olkb/olkb_parts/planck/lo-pro-plate-mx-2x2u.stl

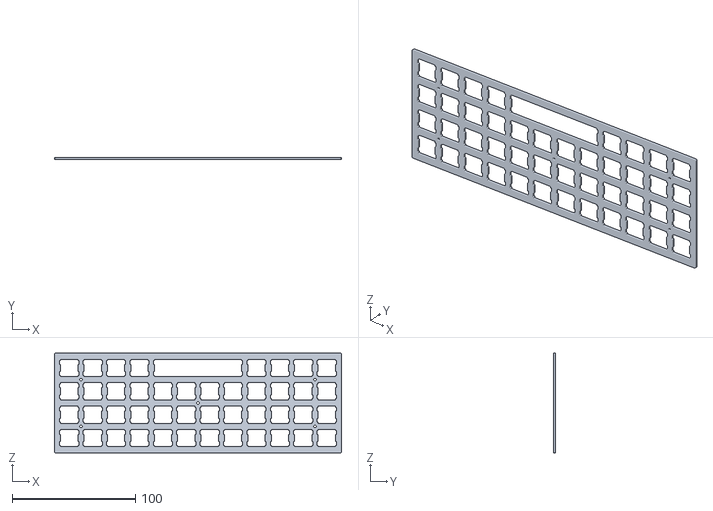
[picture p17: CAD file, 2018-10-09]
planck/lo-pro-plate-mx-2x2u.stl
233.0 x 1.54 x 81.0
