olkb/olkb_parts/planck/middles/MIDPLK50-12.stl

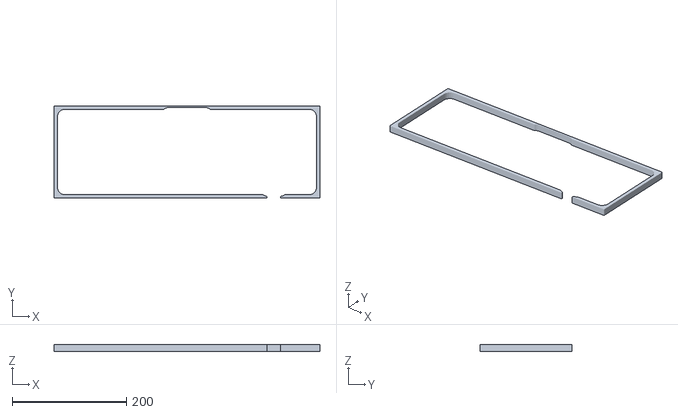
[picture p18: CAD file, 2015-04-01]
planck/middles/MIDPLK50-12.stl
466.0 x 162.0 x 12.0
