olkb/olkb_parts/planck/tops/TOPGRD50.dxf

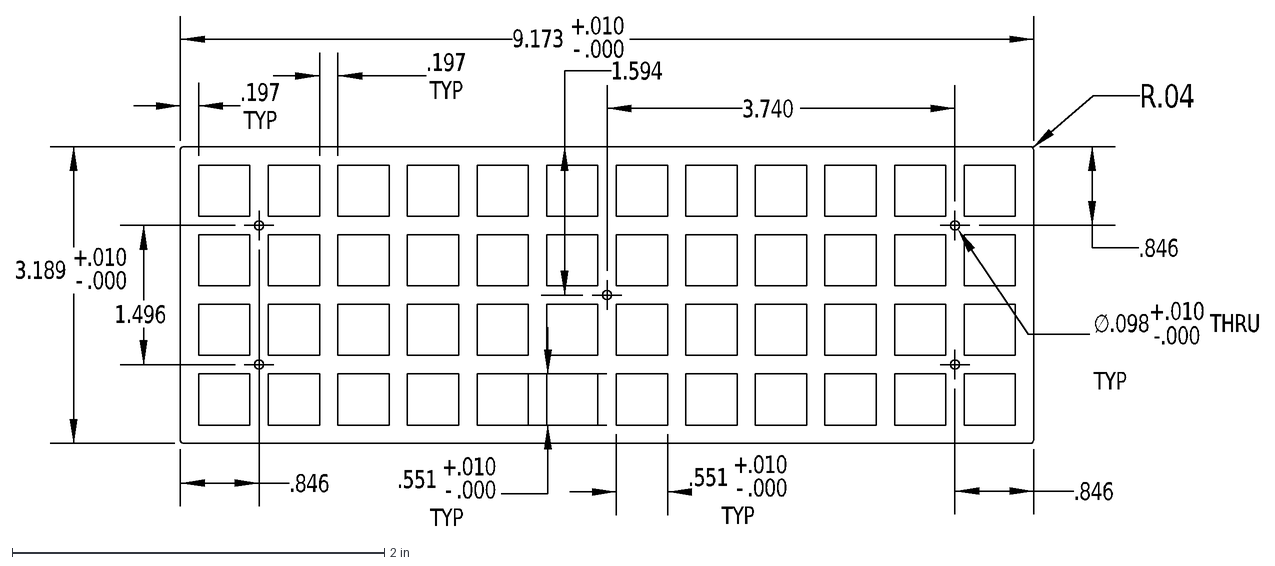
[picture p19: CAD file, 2016-04-22]
planck/tops/TOPGRD50.dxf
9.173
+
-
.010
.000
3.189
∅.098+.010^-.000 THRU TYP
.551
TYP
.197
.846
3.740
1.496
1.594
R.04
