olkb/olkb_parts/preonic/preonic-rev3-hipro-mod.stl

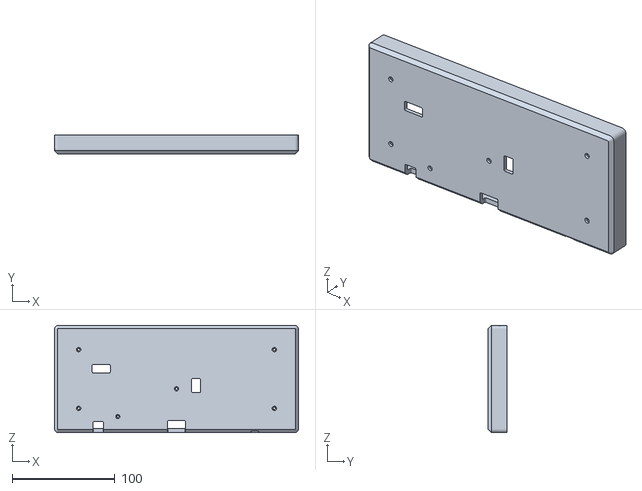
[picture p20: CAD file, 2019-12-29]
preonic/preonic-rev3-hipro-mod.stl
237.0 x 18.1 x 104.0
