olkb/olkb_parts/atomic/tops/TOPJCK50.dxf

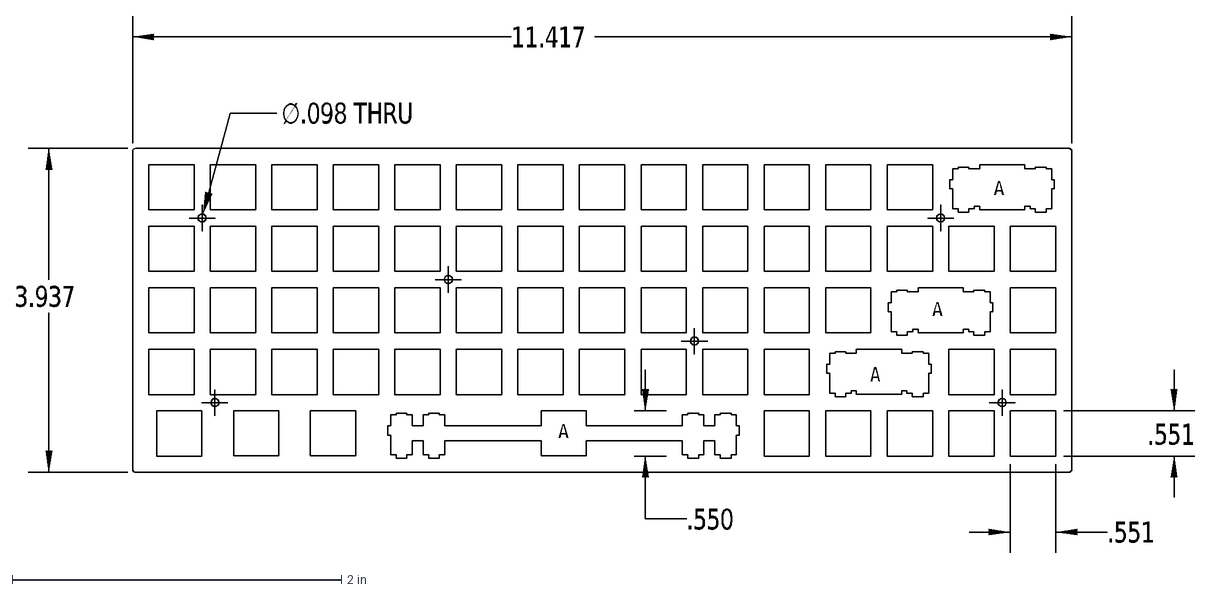
[picture p21: CAD file, 2016-04-22]
atomic/tops/TOPJCK50.dxf
A
11.417
3.937
.551
.550
∅.098 THRU
