olkb/olkb_parts/others/TOPNEU50.dxf

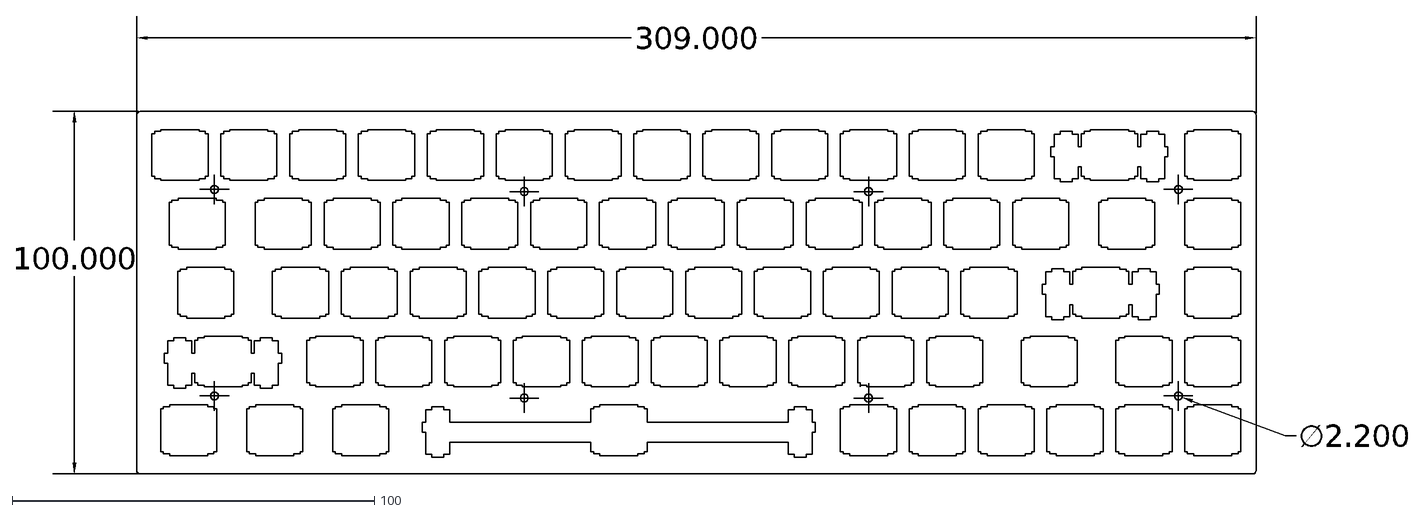
[picture p22: CAD file, 2016-04-22]
others/TOPNEU50.dxf
309.000
100.000
∅2.200
