olkb/olkb_parts/planck/hi-pro-plate-mx.stl

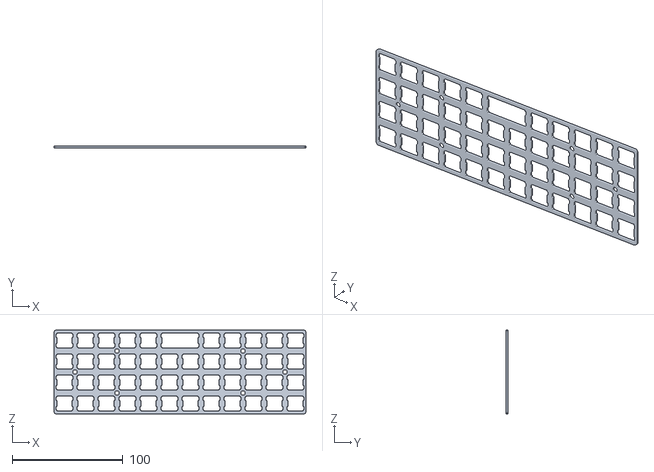
[picture p23: CAD file, 2018-06-27]
planck/hi-pro-plate-mx.stl
228.0 x 1.54 x 76.0
