olkb/olkb_parts/planck/lo-pro-covers/case-cover-plain.stl

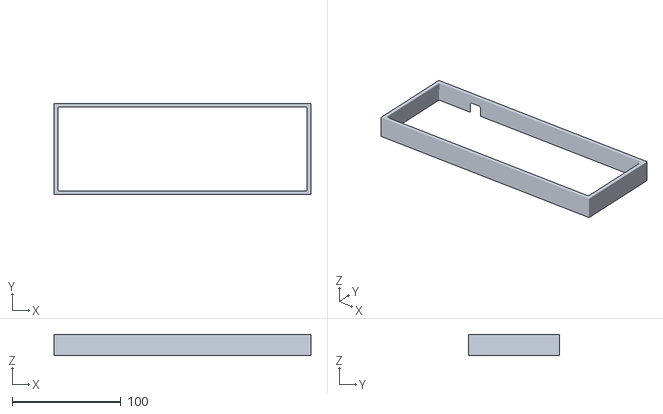
[picture p24: CAD file, 2017-01-22]
planck/lo-pro-covers/case-cover-plain.stl
236.0 x 84.0 x 19.5
