olkb/olkb_parts/planck/middles/MIDPLK50-14.stl

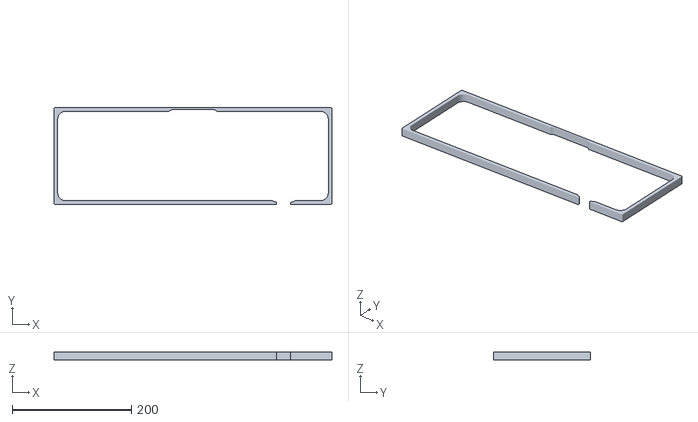
[picture p25: CAD file, 2015-04-01]
planck/middles/MIDPLK50-14.stl
466.0 x 162.0 x 14.0
