olkb/olkb_parts/planck/tops/TOPMIT50.dxf

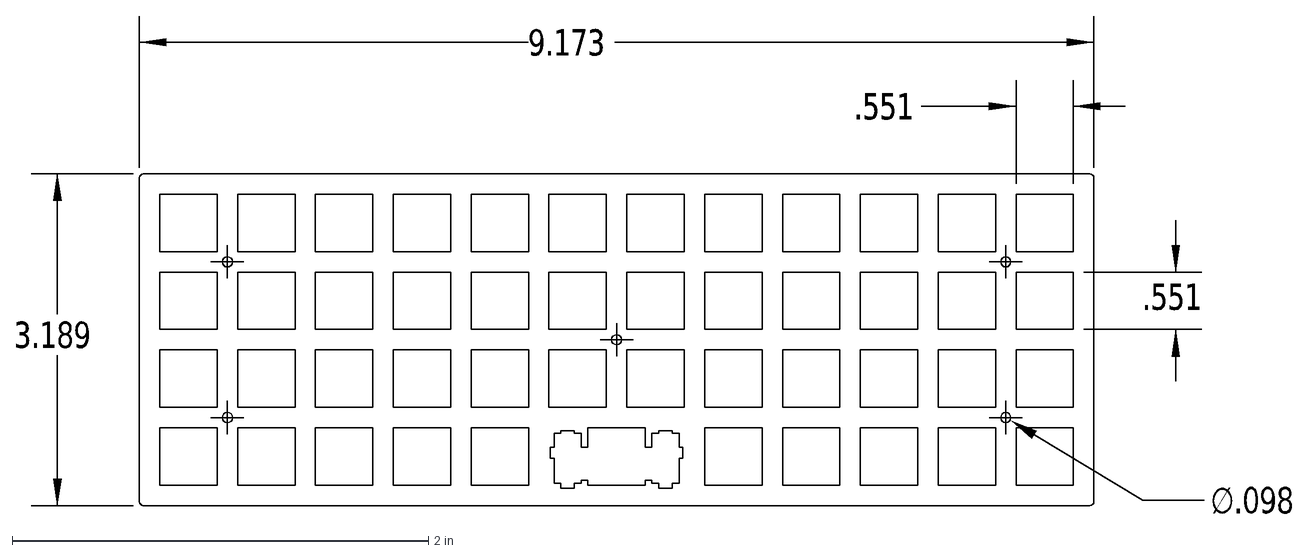
[picture p26: CAD file, 2016-04-22]
planck/tops/TOPMIT50.dxf
9.173
3.189
∅.098
.551
