olkb/olkb_parts/preonic/PRE-END.stl

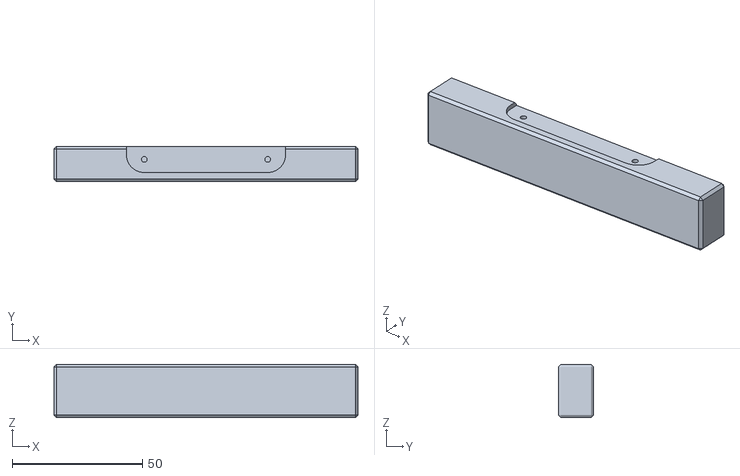
[picture p27: CAD file, 2019-11-19]
preonic/PRE-END.stl
116.5 x 13.5 x 20.5
