olkb/olkb_parts/atomic/tops/TOPASK50.dxf

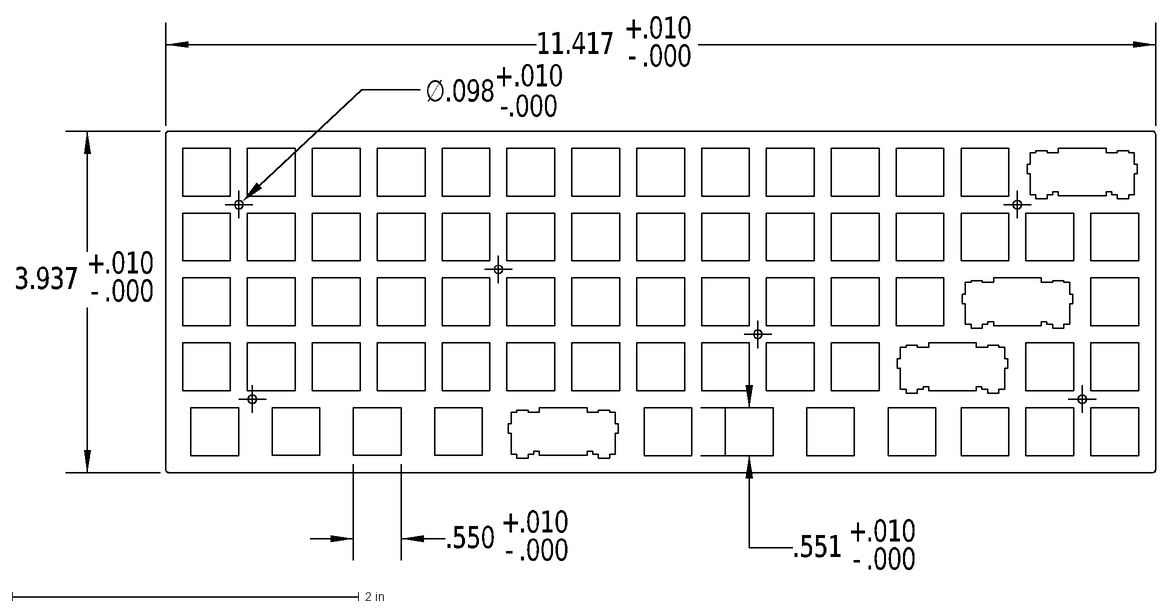
[picture p28: CAD file, 2016-04-22]
atomic/tops/TOPASK50.dxf
11.417
+
-
.010
.000
3.937
.550
.551
∅.098+.010^-.000
