olkb/olkb_parts/others/TOPQUA50.dxf

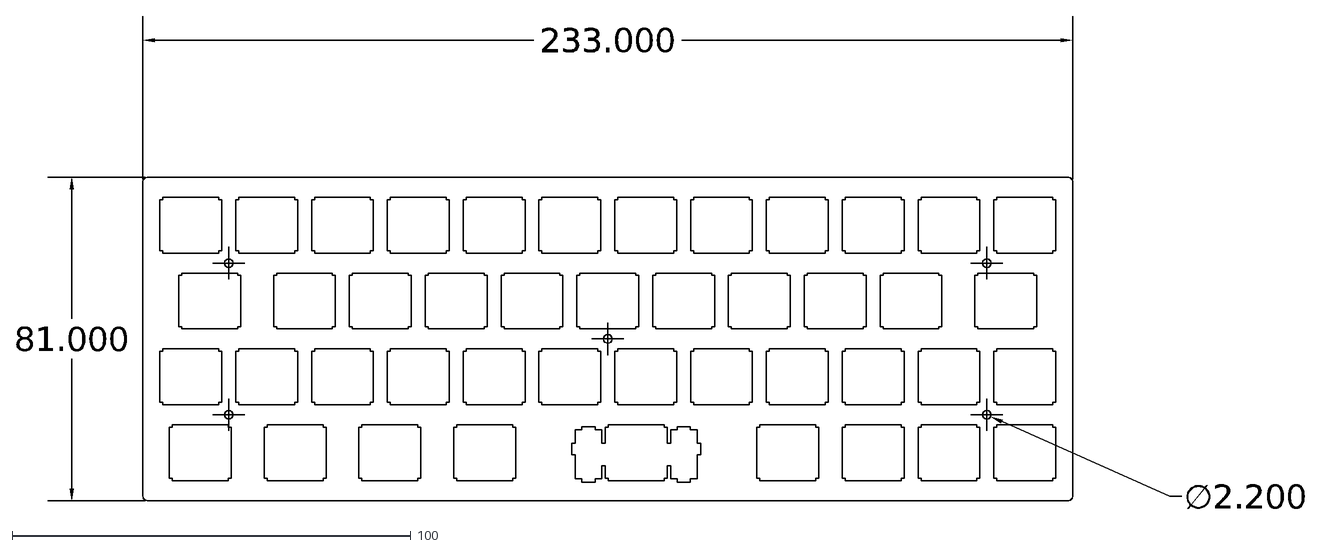
[picture p29: CAD file, 2016-04-22]
others/TOPQUA50.dxf
233.000
81.000
∅2.200
