olkb/olkb_parts/planck/lo-pro-covers/case-cover-high.stl

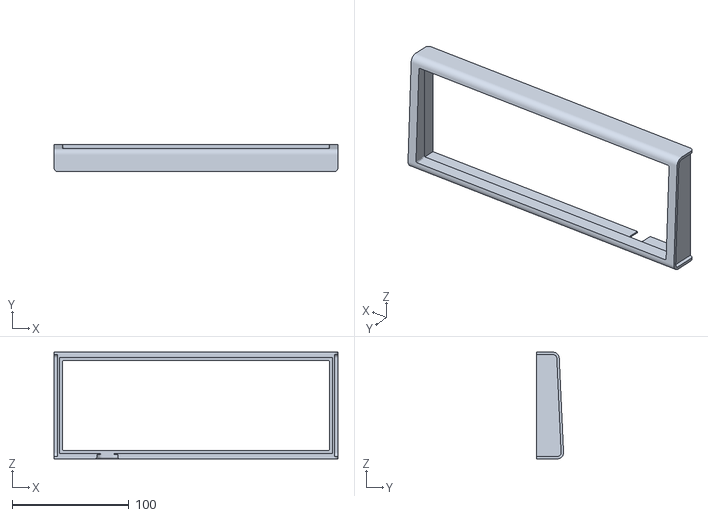
[picture p30: CAD file, 2017-01-06]
planck/lo-pro-covers/case-cover-high.stl
243.4 x 23.3 x 91.4
