olkb/olkb_parts/planck/middles/MIDPLK50-10.stl

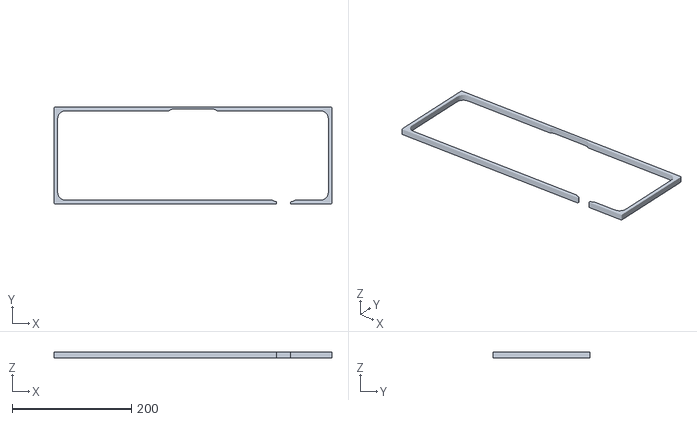
[picture p31: CAD file, 2015-03-30]
planck/middles/MIDPLK50-10.stl
466.0 x 162.0 x 10.00
