olkb/olkb_parts/planck/tops/TOPPMU50.dxf

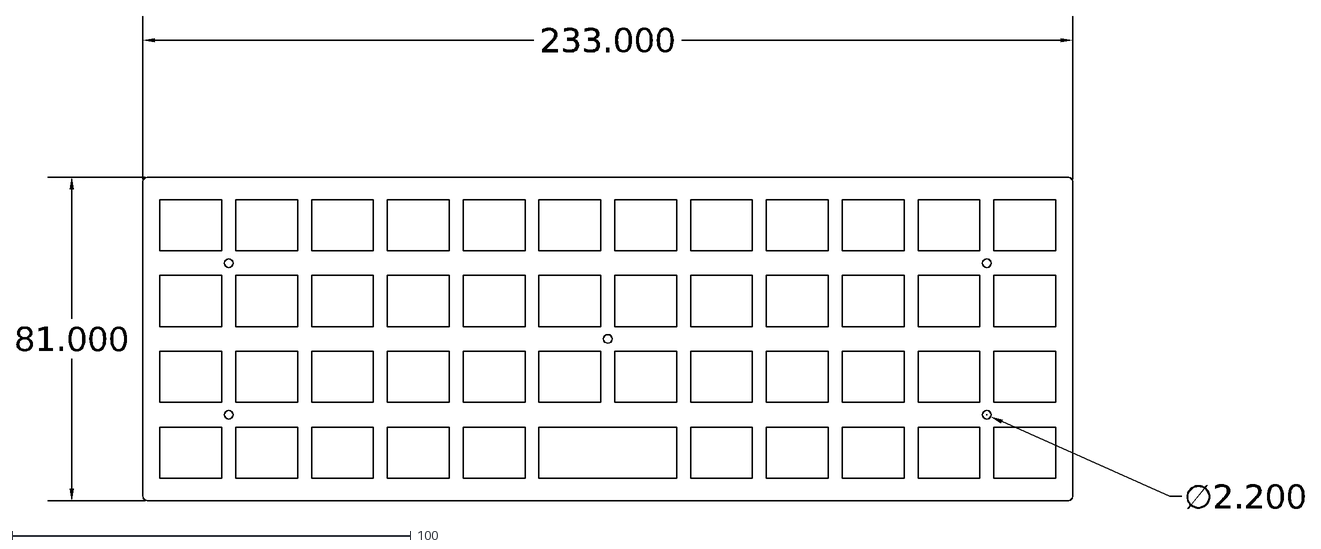
[picture p32: CAD file, 2016-04-22]
planck/tops/TOPPMU50.dxf
233.000
81.000
∅2.200
