olkb/olkb_parts/preonic/hi-pro-plate-mx-2x2u.stl

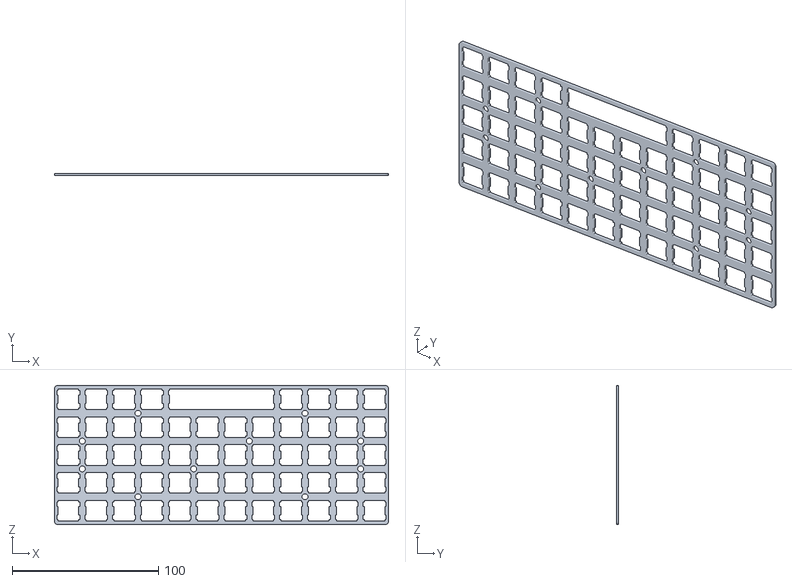
[picture p33: CAD file, 2018-06-27]
preonic/hi-pro-plate-mx-2x2u.stl
228.0 x 1.54 x 95.0
