olkb/olkb_parts/atomic/tops/TOPMLO50.dxf

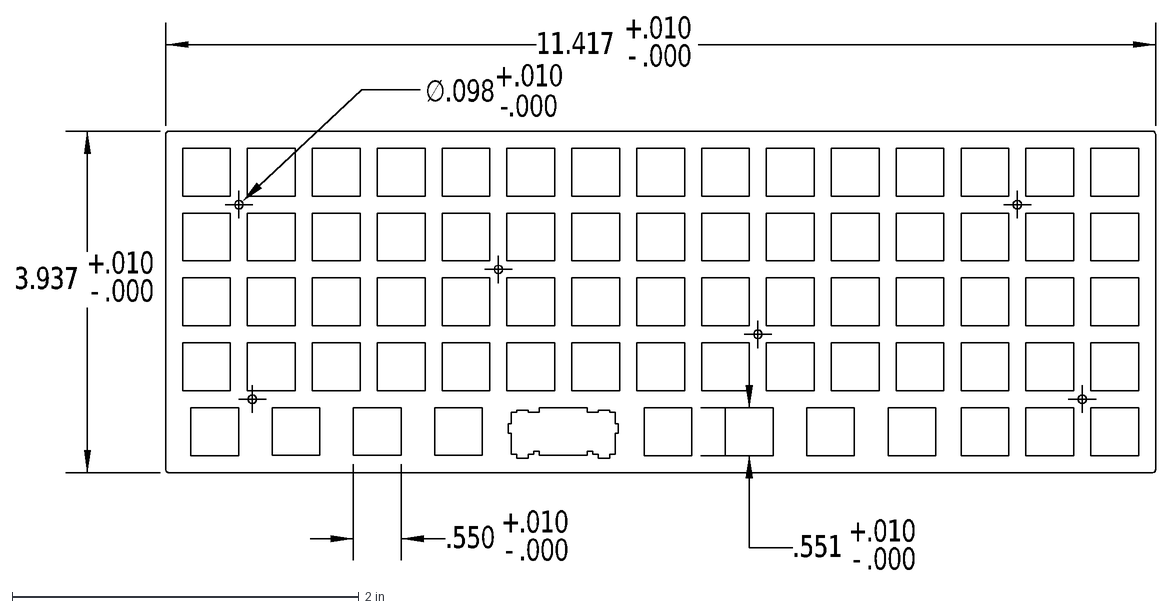
[picture p34: CAD file, 2016-04-22]
atomic/tops/TOPMLO50.dxf
11.417
+
-
.010
.000
3.937
.550
.551
∅.098+.010^-.000
