olkb/olkb_parts/planck/hi-pro-plate-matias.stl

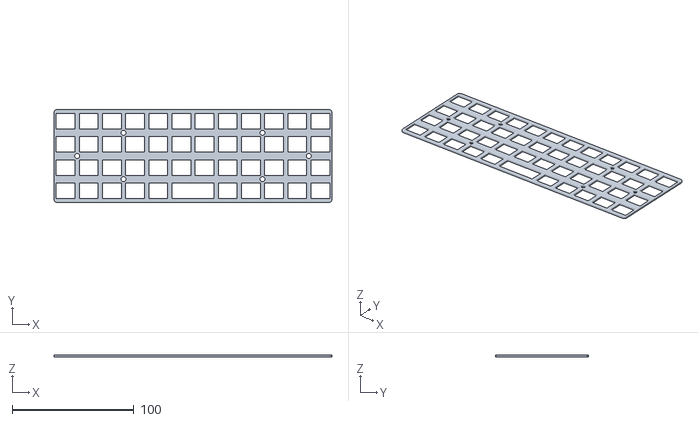
[picture p35: CAD file, 2018-06-27]
planck/hi-pro-plate-matias.stl
228.0 x 76.0 x 1.54
