olkb/olkb_parts/planck/tops/TOPPUN50.dxf

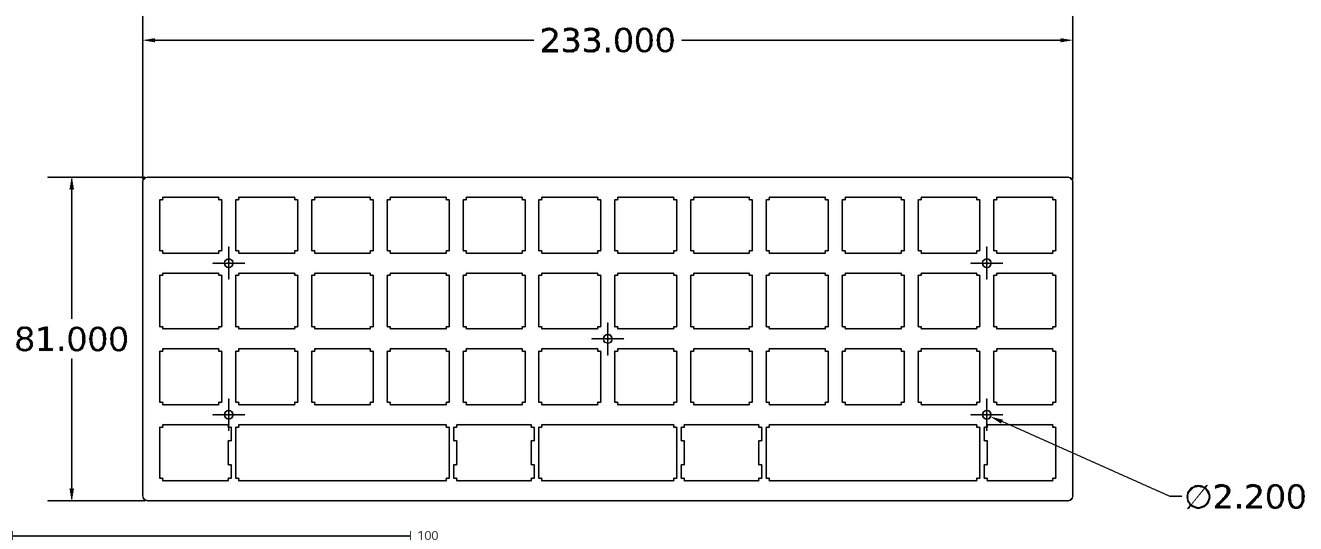
[picture p36: CAD file, 2016-04-22]
planck/tops/TOPPUN50.dxf
233.000
81.000
∅2.200
