olkb/olkb_parts/atomic/tops/TOPMAU50.dxf

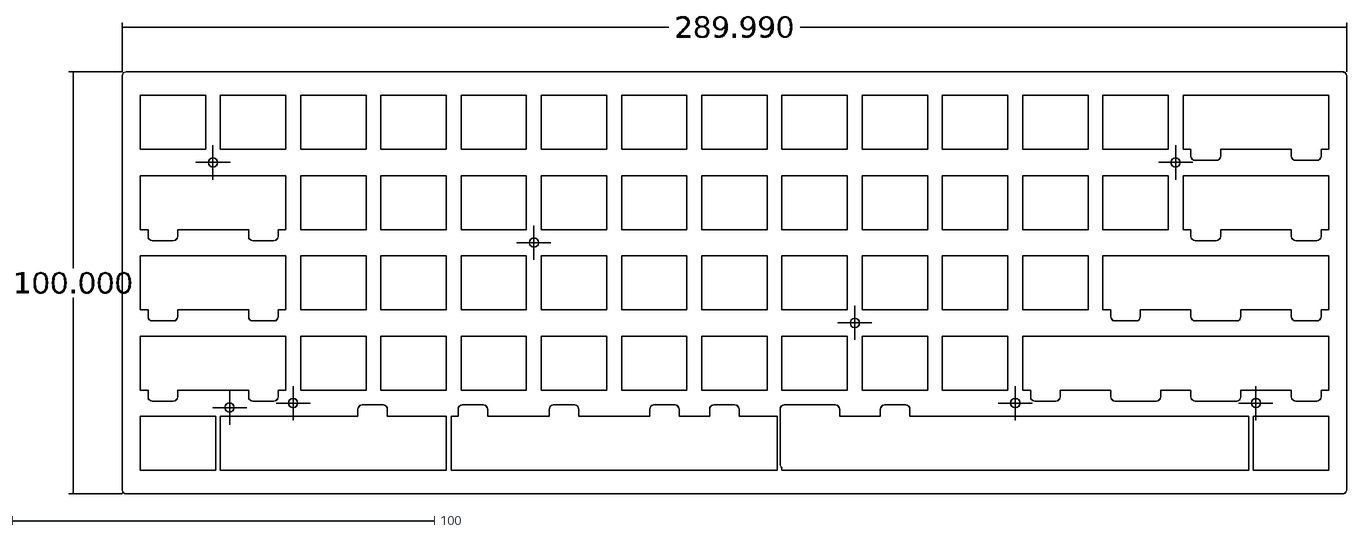
[picture p37: CAD file, 2016-04-22]
atomic/tops/TOPMAU50.dxf
289.990
100.000
