olkb/olkb_parts/planck/hi-pro-bottom.stl

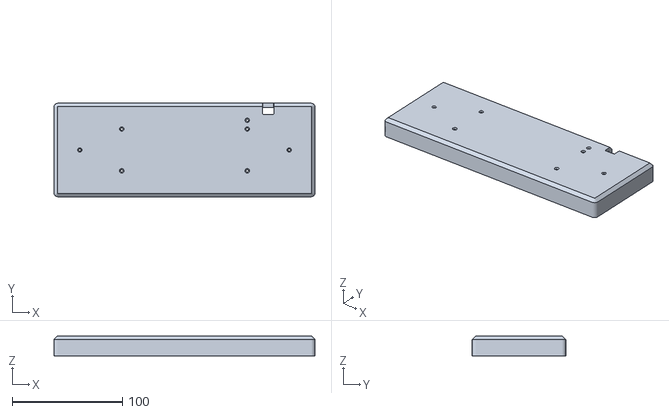
[picture p38: CAD file, 2018-06-27]
planck/hi-pro-bottom.stl
237.0 x 85.0 x 18.1
