olkb/olkb_parts/atomic/tops/TOPAUN50.dxf

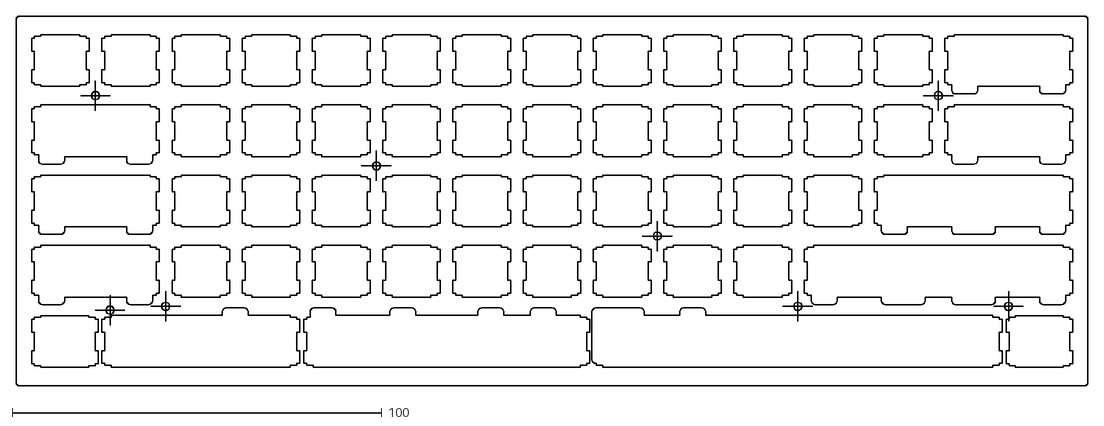
[picture p39: CAD file, 2016-04-22]
atomic/tops/TOPAUN50.dxf
290.0 x 100.0
