olkb/olkb_parts/planck/hi-pro-bottom-mod.stl

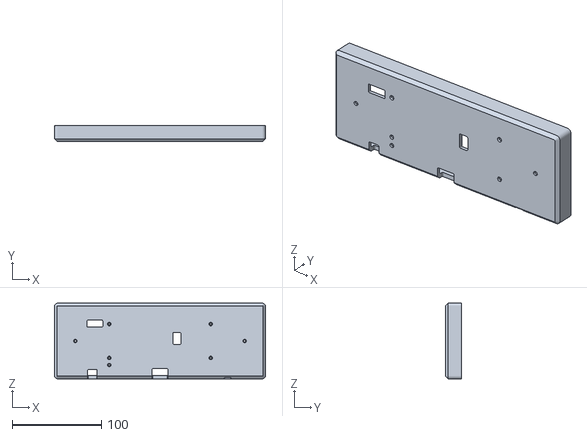
[picture p40: CAD file, 2018-06-27]
planck/hi-pro-bottom-mod.stl
237.0 x 18.1 x 85.0
