olkb/olkb_parts/preonic/hi-pro-bottom-rev3.stl

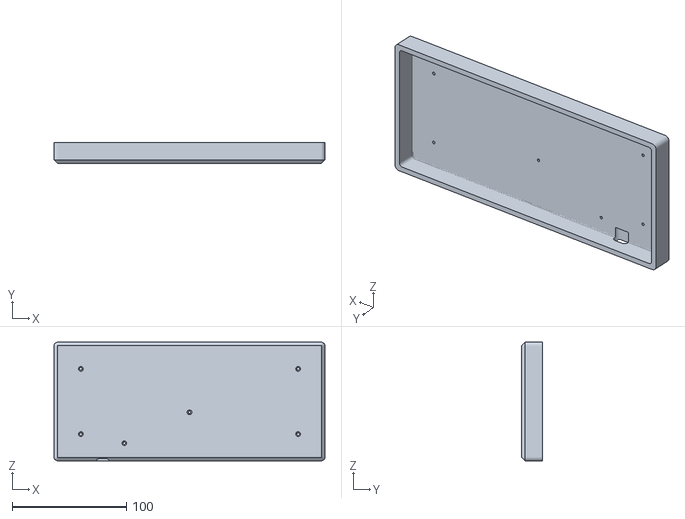
[picture p41: CAD file, 2018-06-27]
preonic/hi-pro-bottom-rev3.stl
237.0 x 18.1 x 104.0
