olkb/olkb_parts/planck/bottom-plate.dxf

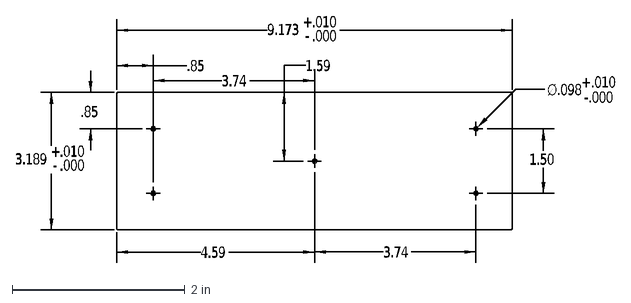
[picture p42: CAD file, 2016-04-22]
planck/bottom-plate.dxf
9.173
+
-
.010
.000
3.189
.85
4.59
1.59
3.74
1.50
∅.098+.010^-.000
