olkb/olkb_parts/planck/lo-pro-bottom.stl

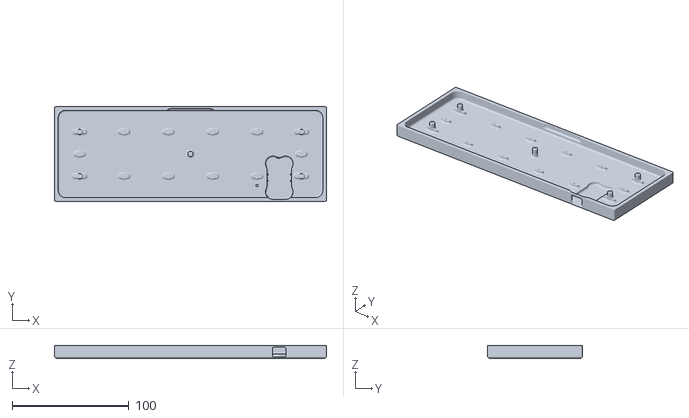
[picture p43: CAD file, 2015-03-30]
planck/lo-pro-bottom.stl
233.0 x 81.0 x 11.5
